incursion64/GP2040-CE-OpenStick-GRC/z_readme assets/IMG_3227.jpg

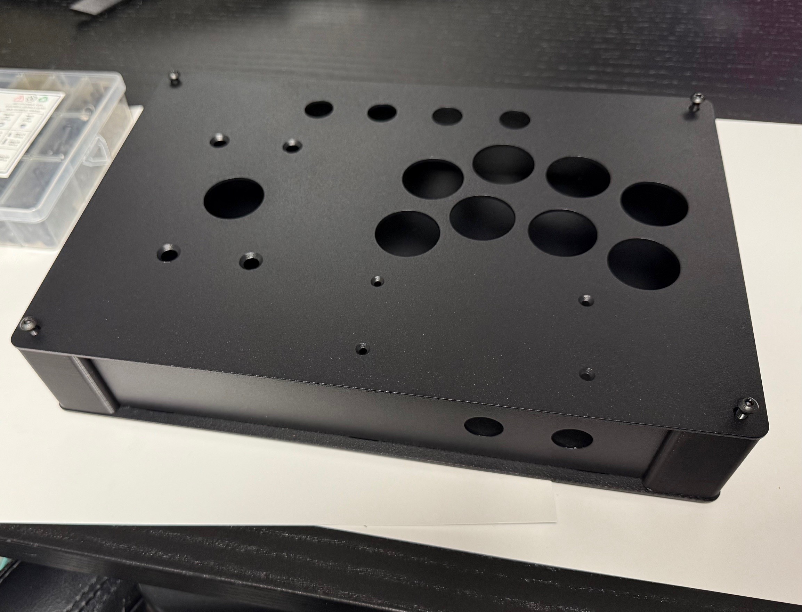
z_readme assets/IMG_3227.jpg
